appositeit/sca-helm/outputs/sweep/baseline/coverage_vs_tooling.png

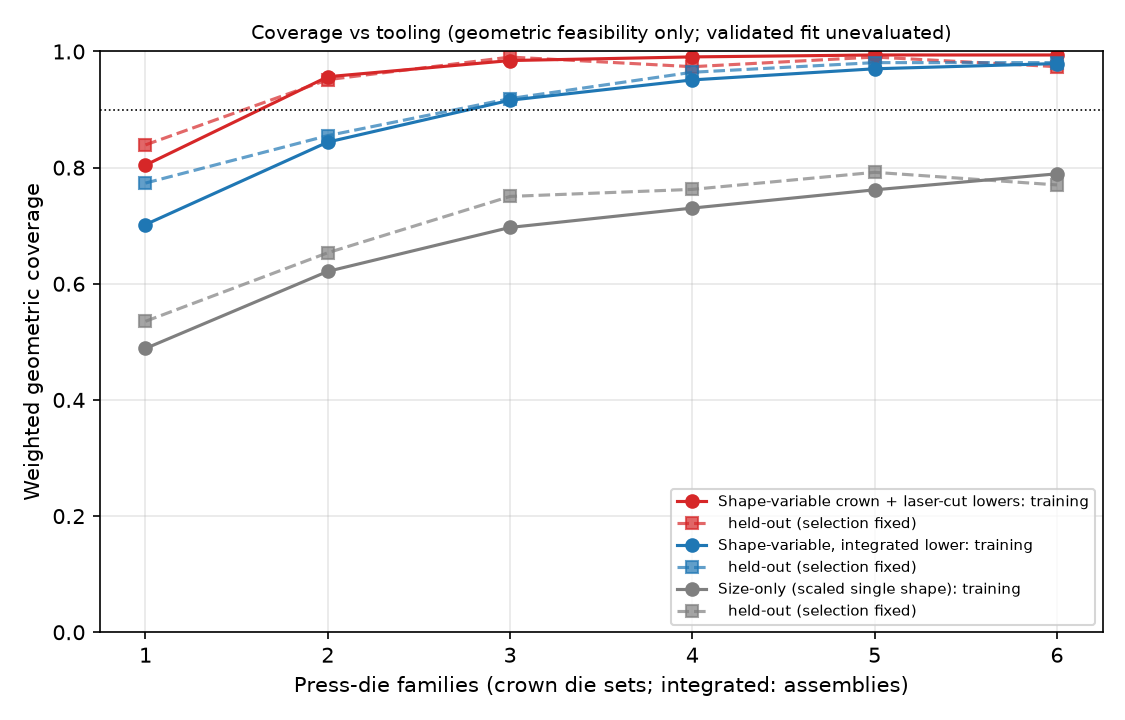
outputs/sweep/baseline/coverage_vs_tooling.png
