appositeit/sca-helm/outputs/sweep/baseline/covered_heads.png

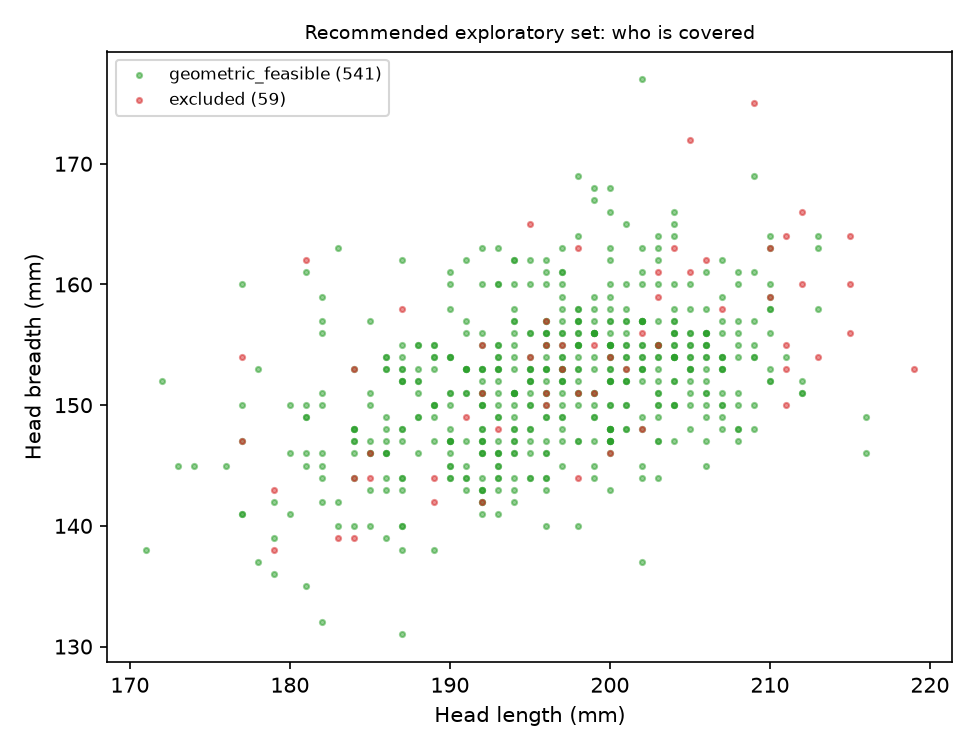
outputs/sweep/baseline/covered_heads.png
