appositeit/sca-helm/outputs/sweep/female_30/coverage_vs_tooling.png

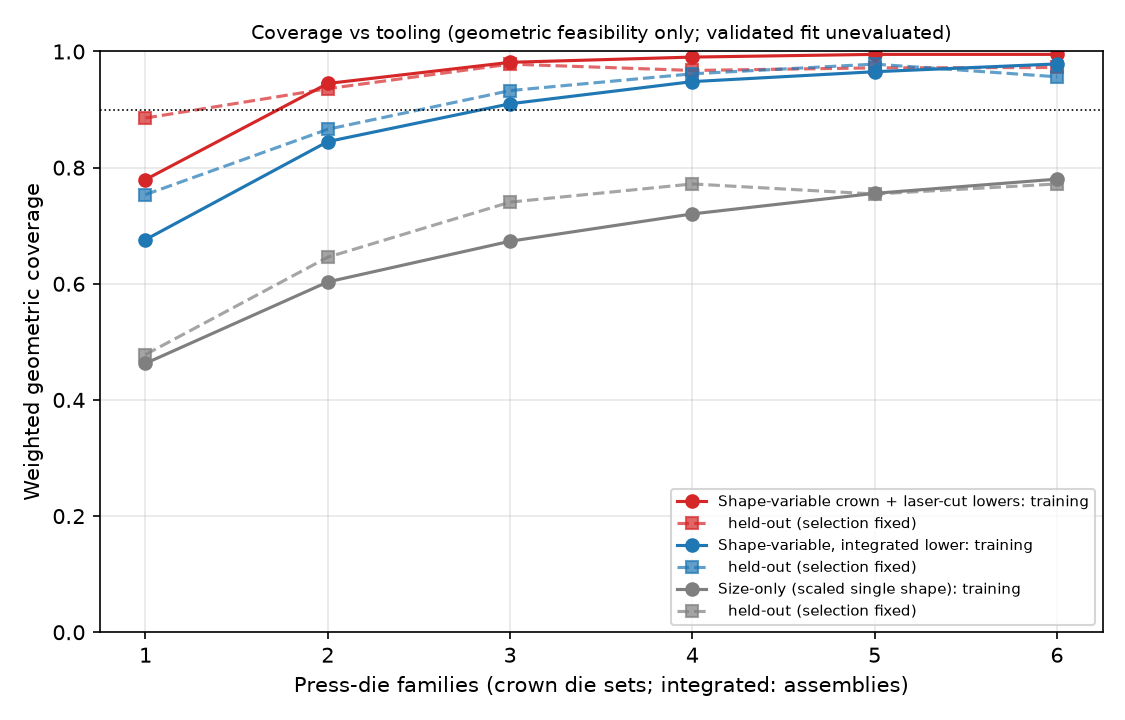
outputs/sweep/female_30/coverage_vs_tooling.png
