appositeit/sca-helm/outputs/sweep/liner_depth_35/coverage_vs_tooling.png

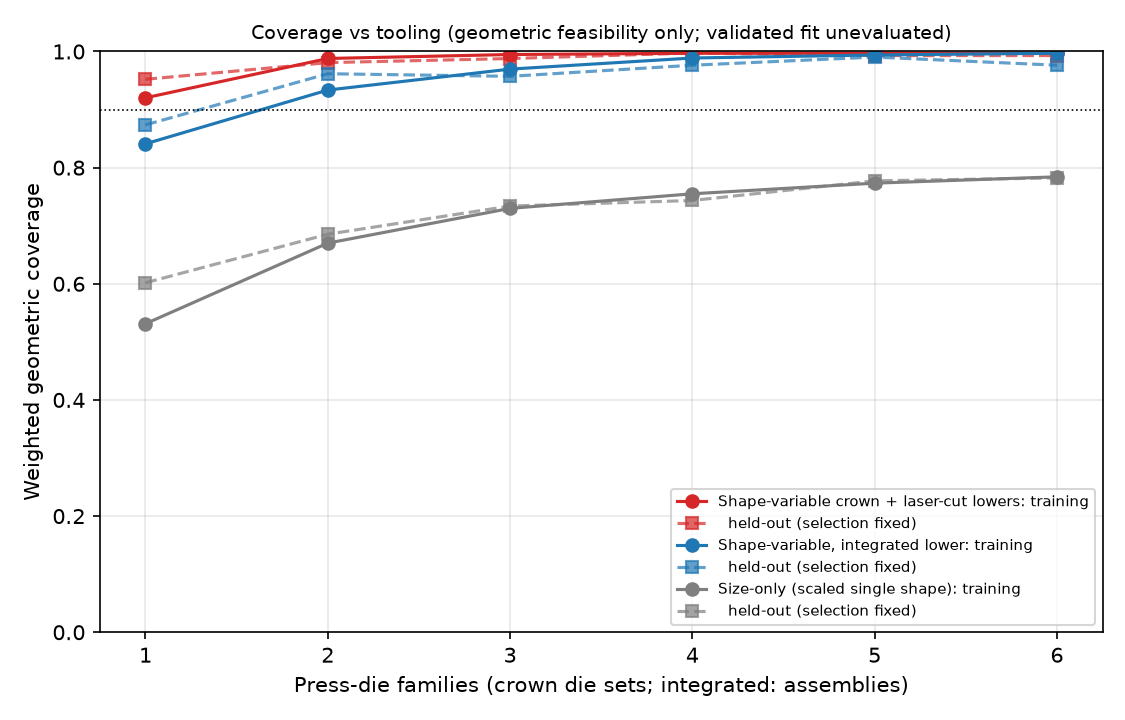
outputs/sweep/liner_depth_35/coverage_vs_tooling.png
