appositeit/sca-helm/outputs/sweep/pressure_band_wide/coverage_vs_tooling.png

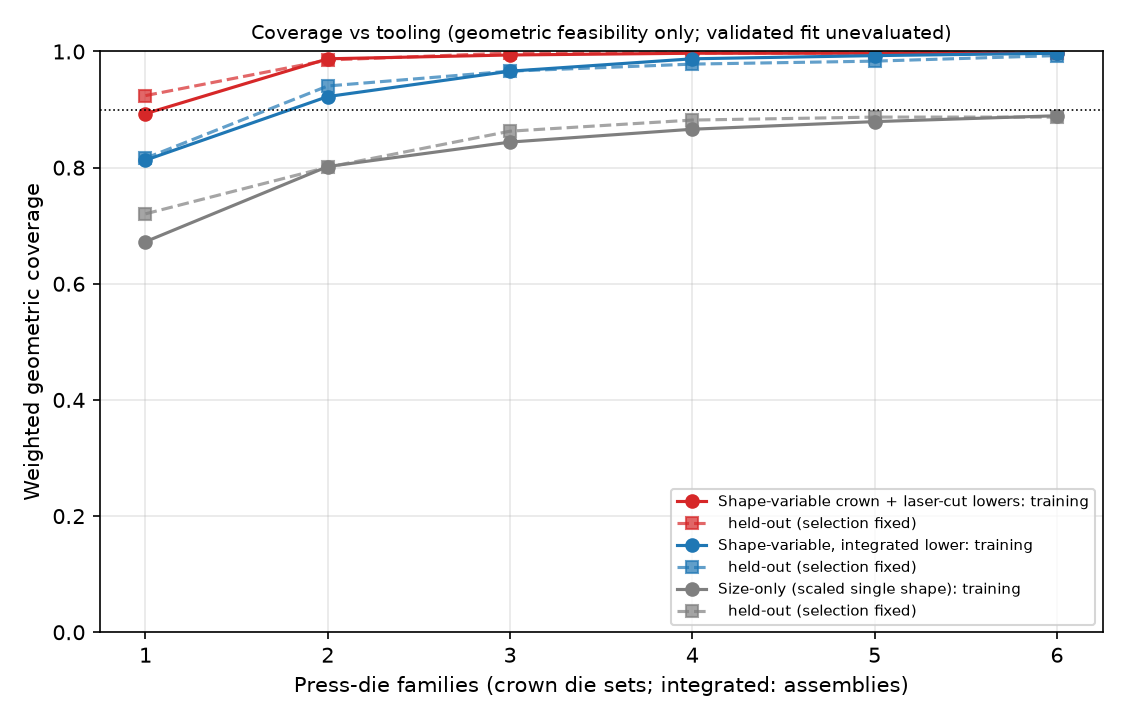
outputs/sweep/pressure_band_wide/coverage_vs_tooling.png
