appositeit/sca-helm/outputs/sweep/shape_prior_wide/coverage_vs_tooling.png

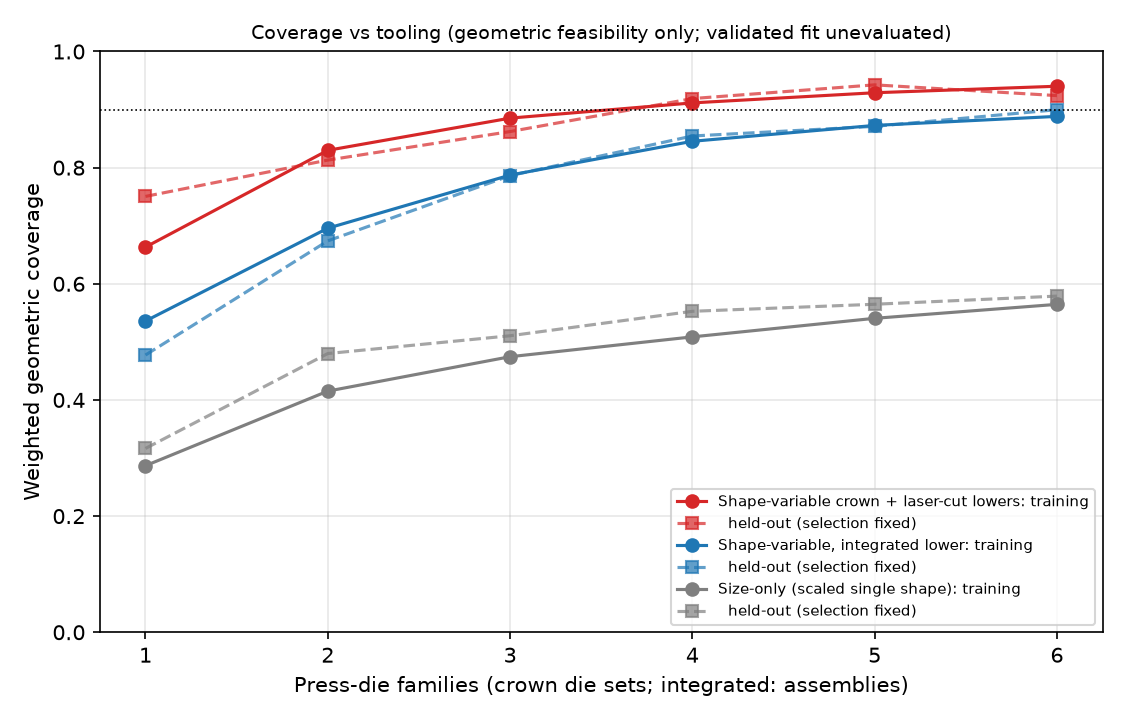
outputs/sweep/shape_prior_wide/coverage_vs_tooling.png
