appositeit/sca-helm/outputs/sweep/tolerance_loose/coverage_vs_tooling.png

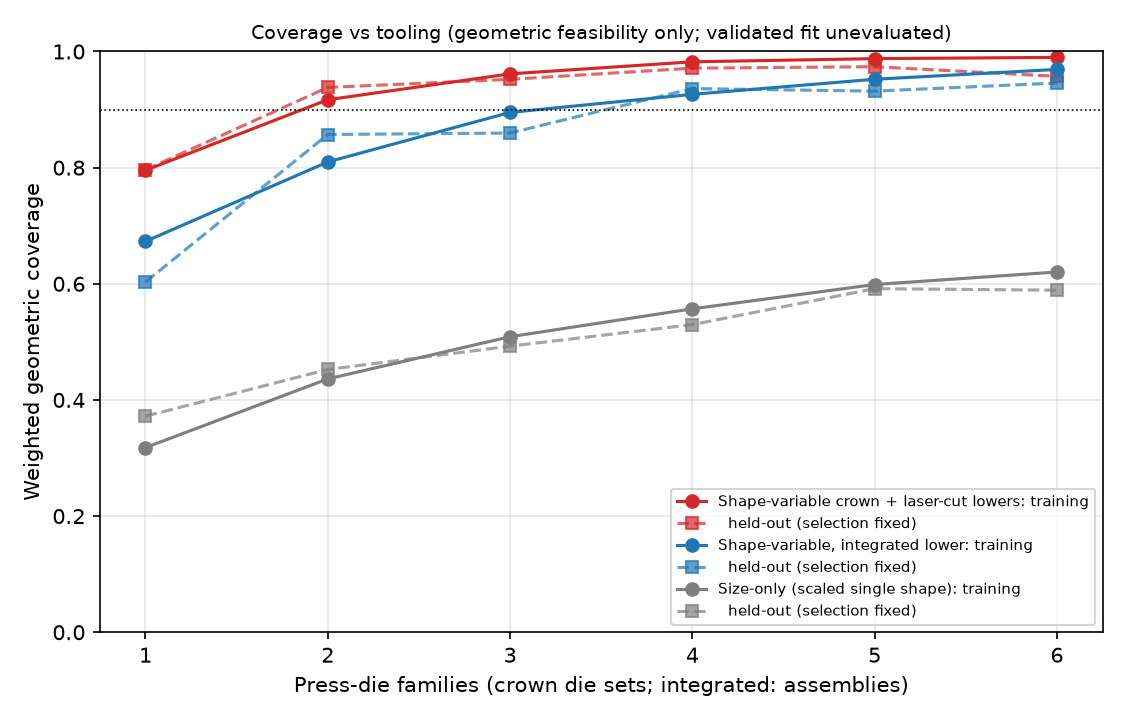
outputs/sweep/tolerance_loose/coverage_vs_tooling.png
