appositeit/sca-helm/outputs/sweep/tolerance_tight/coverage_vs_tooling.png

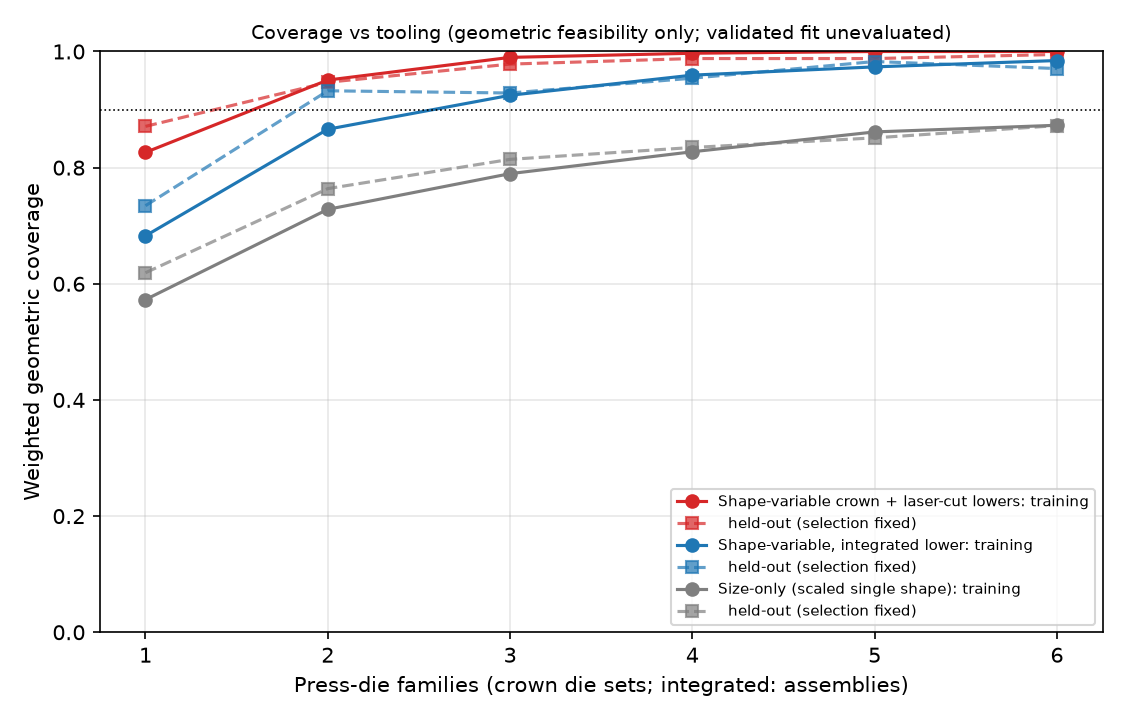
outputs/sweep/tolerance_tight/coverage_vs_tooling.png
