appositeit/sca-helm/outputs/sweep/liner_depth_35/excluded_characteristics.csv

sex | status | n | head_length_mean | head_breadth_mean | head_circumference_mean | tragion_top_mean | menton_sellion_mean
F | excluded | 31 | 183.8 | 143.4 | 540.3 | 120.0 | 109.1
F | geometric_feasible | 165 | 190.8 | 148.0 | 562.2 | 127.8 | 113.2
M | excluded | 27 | 197.6 | 155.9 | 574.6 | 134.2 | 122.7
M | geometric_feasible | 377 | 199.9 | 154.3 | 574.6 | 131.0 | 122.8
all | reason:pad_too_loose | 27
all | reason:field_of_view | 22
all | reason:pad_too_tight | 7
all | reason:pad_between_steps | 2
